NorthernWidget-Skunkworks/Project-Tally/Development/CapacitorPowerCharger.asc

C1: cap; .22; IC = 0
D1: diode; 1N4001
D2: zener; MMSZ4683
R1: res; 10
V1: voltage; 3.3
Named nets: 0
.MODEL 1N4001 d
+IS=5.31656e-08 RS=0.0392384 N=2 EG=0.6
+XTI=0.05 BV=400 IBV=5e-08 CJO=1e-11
+VJ=0.7 M=0.5 FC=0.5 TT=1e-09
+KF=0 AF=1
.MODEL MMSZ4683 D (BV = 3 IBV = 0.05m)
.tran 20
