NorthernWidget-Skunkworks/Project-Tally/Development/LineControlCircuit.asc

C1: cap; {C_Int}
C2: cap; {C_Int}
C3: cap; {C_Int}
C4: cap; {C_Int}
M1: nmos; 2N7002
M2: nmos; 2N7002
M3: pmos; FDC638P
M4: nmos; IRF6201
M5: nmos; 2N7002
M6: pmos; FDC638P
R1: res; 10k
R2: res; 1k
R3: res; {R_f}
R4: res; 10k
R5: res; {R_f}
R6: res; 10k
R7: res; 20k
R8: res; {R_f}
R9: res; 10k
R10: res; {R_f}
U1: LTC2054
U2: LTC2054
U3: LTC2054
U4: LTC2054
V1: voltage; 3.3
V2: voltage; PULSE(0 3.3 10e-4 1e-9 1e-9 10e-3 20e-3 1)
V3: voltage; -3.3
Named nets: Vcc, 0, -Vcc, Pulse
.tran 200e-3
.param R_f = 10k
.param C_Int = 1u
