NorthernWidget-Skunkworks/Project-Tally/Development/PulseLengthTrigger.asc

A1: inv
A2: inv
C1: cap; {mc(1µ, C_tol)}
M1: nmos; 2N7002
R1: res; {mc(10k, R_tol)}
R2: res; {mc(30k, R_tol)}
R3: res; {mc(10k, R_tol)}
U1: LTC2054
V1: voltage; PULSE(0 3.3 1e-3 1e-9 1e-9 10e-3 20e-3 1)
V2: voltage; 3.3
Named nets: 0, Vcc, VRef
.tran 25e-3
.param C_tol = 0.2
.param R_tol = 0.05
.step param run 1 10 1
